mmorub/OptimalControlRcProject/ArduinoSender/Fritzing/Pictures/RF901-Arduino-3.jpg

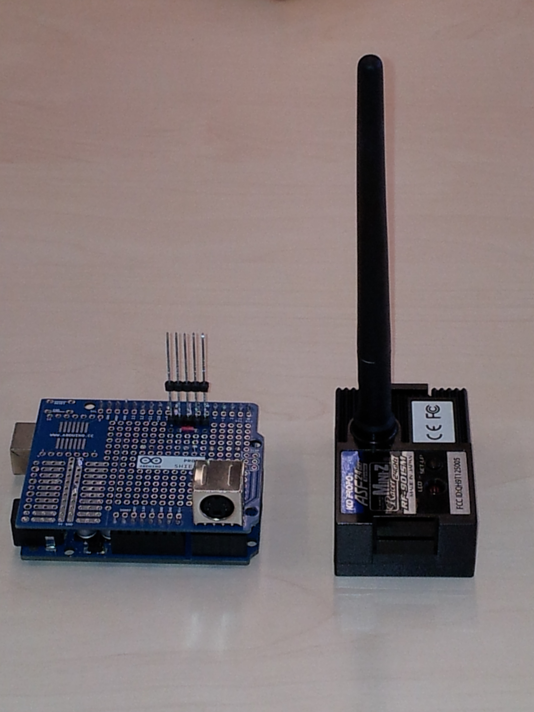
ArduinoSender/Fritzing/Pictures/RF901-Arduino-3.jpg
