mmorub/OptimalControlRcProject/ArduinoSender/Fritzing/Pictures/RF901-Arduino-4.jpg

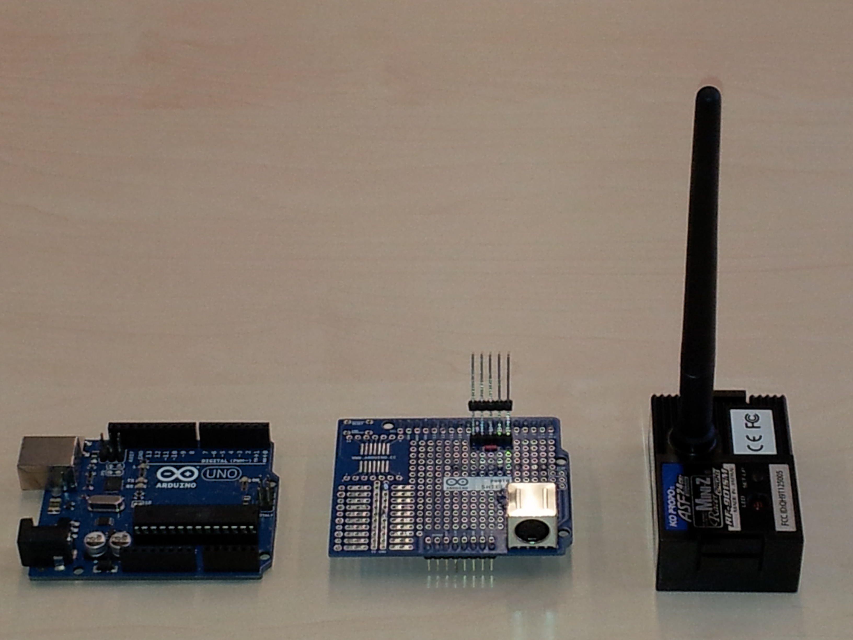
ArduinoSender/Fritzing/Pictures/RF901-Arduino-4.jpg
