mmorub/OptimalControlRcProject/Snippets/arduino/Breadboard/ArduinoAndBreadboardSteerMiniz.jpg

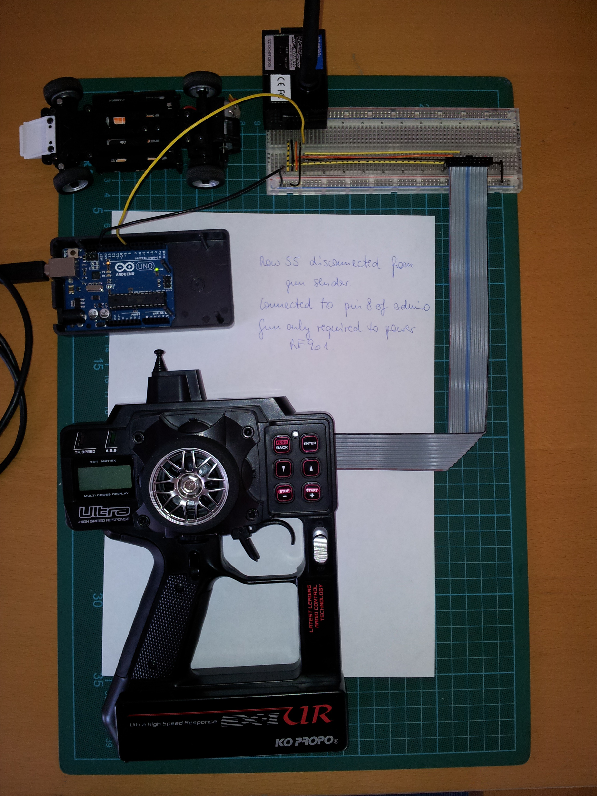
Snippets/arduino/Breadboard/ArduinoAndBreadboardSteerMiniz.jpg
