mmorub/OptimalControlRcProject/Snippets/arduino/Breadboard/Breadboard1.jpg

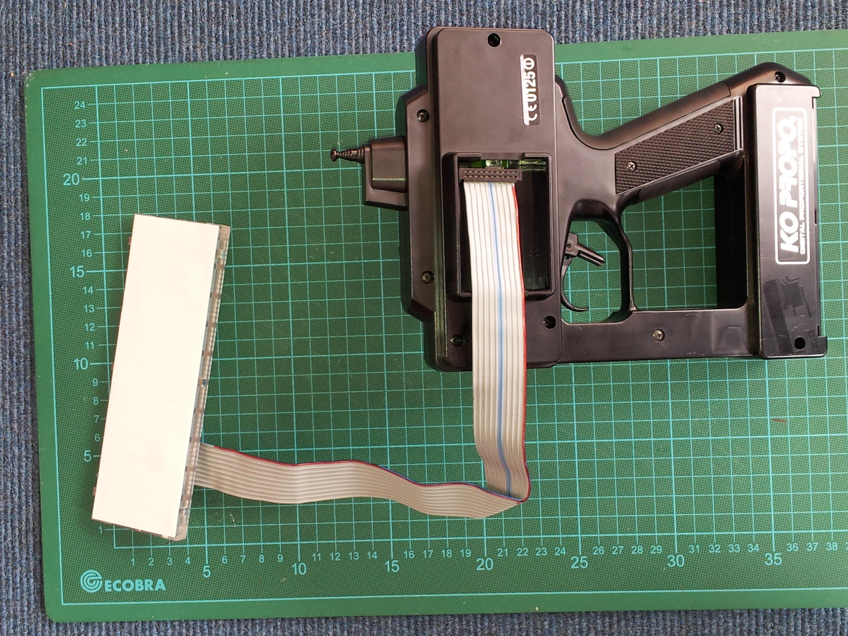
Snippets/arduino/Breadboard/Breadboard1.jpg
