mmorub/OptimalControlRcProject/Snippets/arduino/Breadboard/Breadboard2.jpg

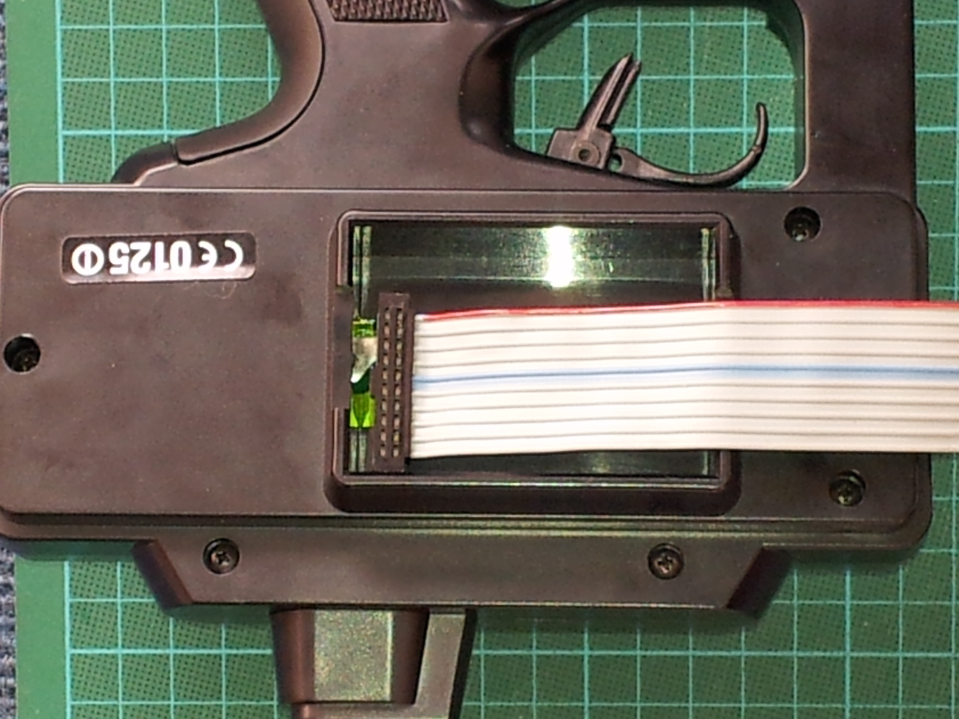
Snippets/arduino/Breadboard/Breadboard2.jpg
