mmorub/OptimalControlRcProject/Snippets/arduino/Breadboard/Breadboard3.jpg

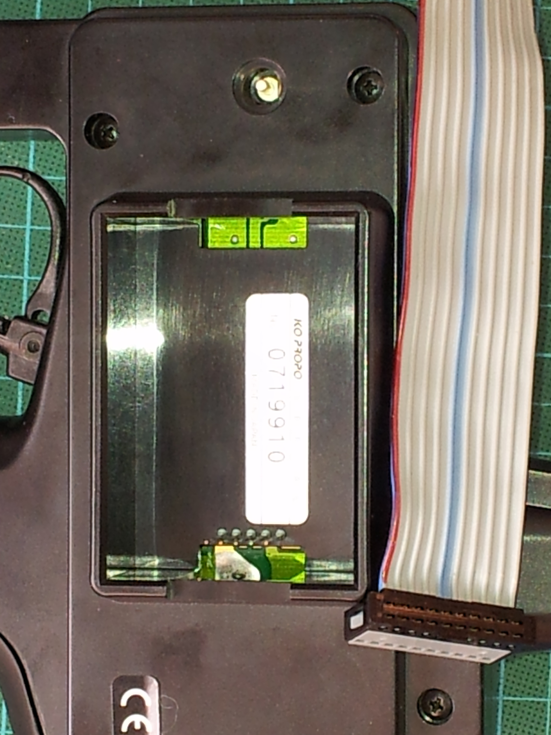
Snippets/arduino/Breadboard/Breadboard3.jpg
