mmorub/OptimalControlRcProject/Snippets/arduino/Breadboard/Breadboard4.jpg

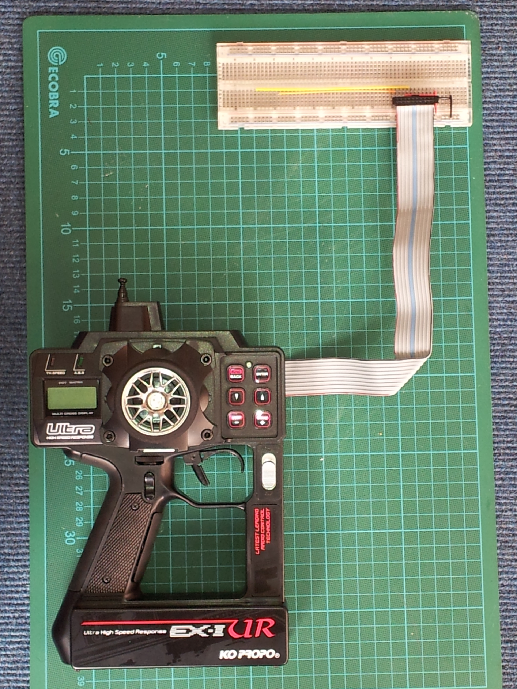
Snippets/arduino/Breadboard/Breadboard4.jpg
