mmorub/OptimalControlRcProject/Snippets/arduino/Breadboard/Breadboard5.jpg

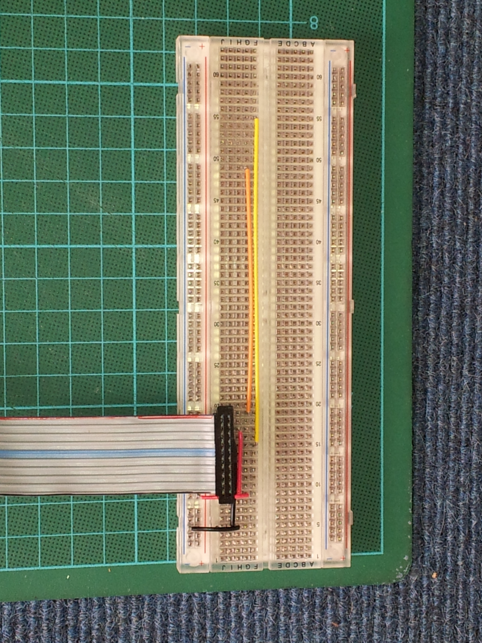
Snippets/arduino/Breadboard/Breadboard5.jpg
