mmorub/OptimalControlRcProject/Snippets/arduino/Breadboard/Breadboard6.jpg

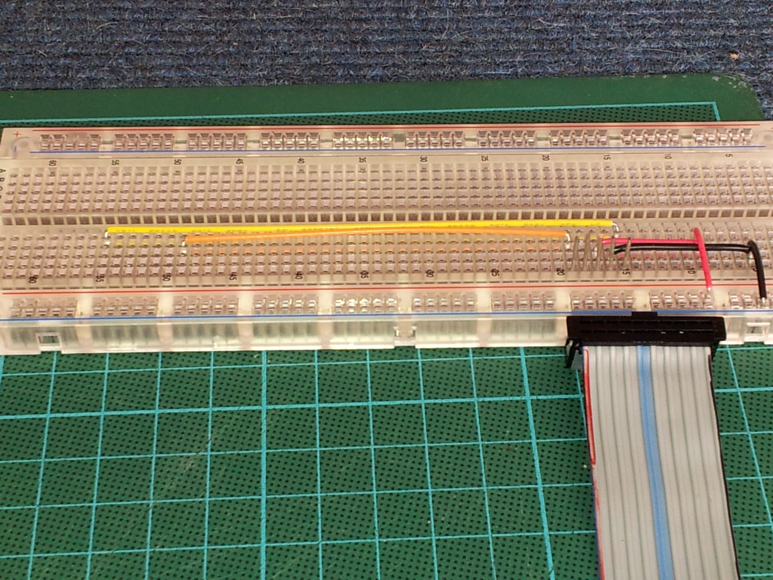
Snippets/arduino/Breadboard/Breadboard6.jpg
