mmorub/OptimalControlRcProject/Snippets/arduino/Breadboard/GunSenderAndBreadboardSteerMiniz.jpg

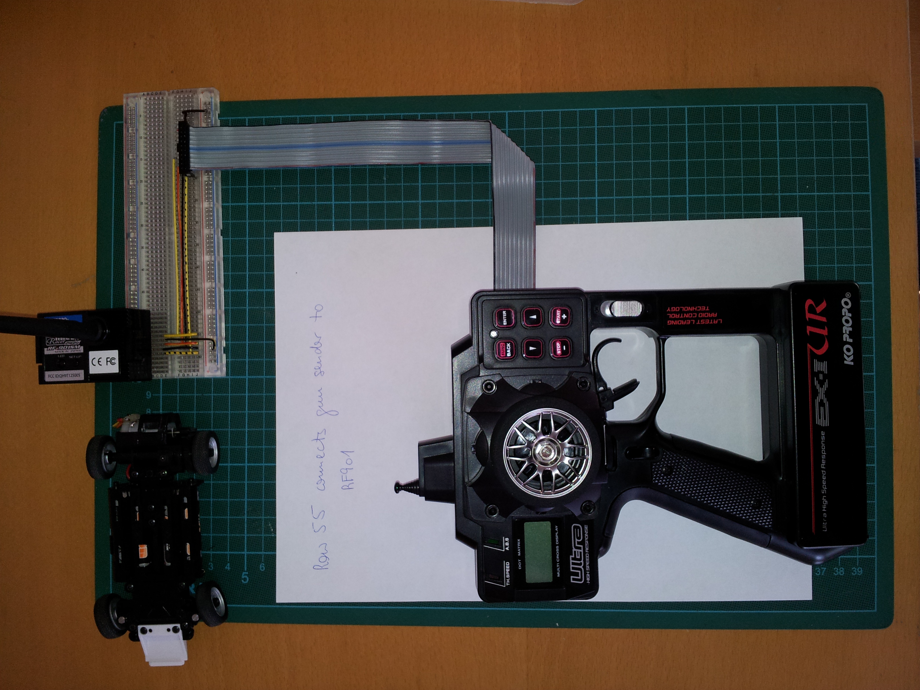
Snippets/arduino/Breadboard/GunSenderAndBreadboardSteerMiniz.jpg
